andrew-albritton/edgetpu-yolo/403_group_presentation_and_Notes_folder/ECEN 403 Capstone Project/Untitled drawing.jpg

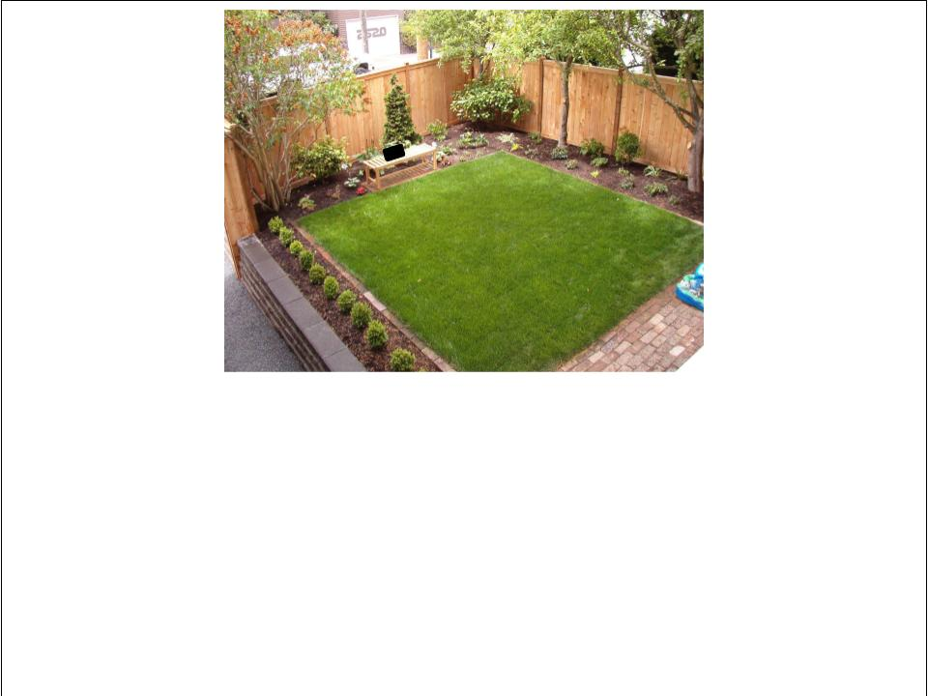
403_group_presentation_and_Notes_folder/ECEN 403 Capstone Project/Untitled drawing.jpg
