andrew-albritton/edgetpu-yolo/403_group_presentation_and_Notes_folder/ECEN 403 Capstone Project/Research/Power System Notes_Links.docx

Basic 5V Supply Example - https://jayconsystems.com/blog/basic-5v-power-supply

DIY Battery Pack - https://preppinginsider.com/diy-lithium-batteries/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,Final%20Assembly%20...%206%20Step%206%3A%20Testing%20

Battery tutorial - https://www.instructables.com/DIY-Professional-18650-Battery-Pack/

Battery Charger Tutorial - https://www.instructables.com/How-to-Make-Battery-Charger-at-Home-1/

Understanding Battery Management Systems - https://www.engineersgarage.com/understanding-battery-management-systems/

Power Bank tutorial - https://climatebiz.com/diy-battery-bank/

IEEE Battery Chargers Paper - https://ieeexplore.ieee.org/document/7870048

DC Jack Drawing Tip - https://electronics.stackexchange.com/questions/2381/deciphering-a-dc-jack-schematic

Parts

Using Li Ion

Need a battery charger IC

Possible Batteries - https://www.amazon.com/1%EF%BF%B58%EF%BF%B56%EF%BF%B550-Rechargeable-Batter%EF%BF%B5y-4000mAh-Batteries/dp/B0C8FLCD9C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

https://www.digikey.com/en/products/detail/microchip-technology/MCP73811T-420I-OT/1626617

https://www.digikey.com/en/products/detail/jauch-quartz/LI18650JP2S1P-PCM-2-WIRES-70MM/9560970

https://www.digikey.com/en/products/detail/analog-devices-inc/LTC2941IDCB-TRMPBF/2238460

Possible BMS - https://www.amazon.com/dp/B07RKL438C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 (https://www.amazon.com/dp/B07RKL438C?s=aht&sp_csd=d2lkZ2V0TmFtZT1zcF9kZXRhaWw)

Other Possible BMS - https://www.amazon.com/11-1V-Balance-Lithium-Battery-Protection/dp/B07JMY631D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

Possible Battery cell holder - https://www.amazon.com/ACEIRMC-Lithium-Battery-Plastic-Cylindrical/dp/B09BFNN1XH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

Nickel Strips - https://www.amazon.com/0-15x6x50mm-Soldering-Capacity-U-S-Solid/dp/B07811NCH3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

Possible DC to DC Step Down converter - https://www.amazon.com/HiLetgo-DC-DC-Module-Charger-Arduino/dp/B01HXU1C6U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

AC to DC Step Down Converter https://www.amazon.com/NOYITO-Precision-100V-264V-Step-Down-Ultra-Small/dp/B07FNJZ1PR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

BMS/Charger Combo Circuit - https://www.amazon.com/AITIAO-Lithium-Battery-Protection-Balance/dp/B0B9MLS51W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

Battery Charger - https://www.ti.com/lit/ds/symlink/bq25792.pdf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

DC/DC Converter (Buck/Boost) - https://www.ti.com/lit/ds/symlink/tps63070.pdf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
